ClemRz/tanduino/bitmaps/P1200767.JPG

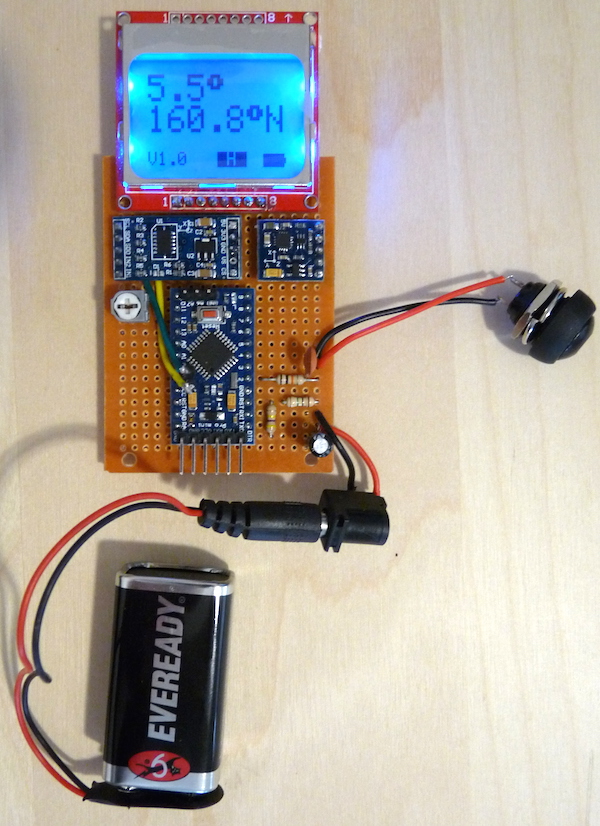
bitmaps/P1200767.JPG
