ClemRz/tanduino/bitmaps/P1200768.JPG

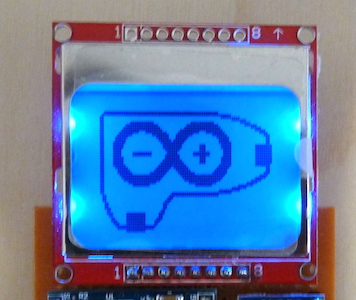
bitmaps/P1200768.JPG
