ClemRz/tanduino/bitmaps/P1200815.JPG

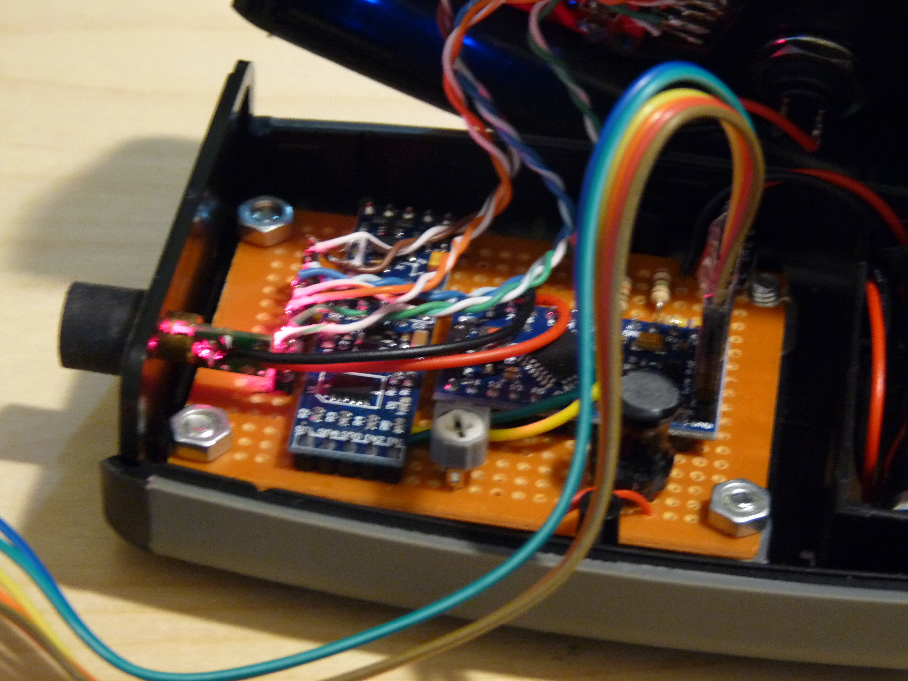
bitmaps/P1200815.JPG
