ClemRz/tanduino/bitmaps/P1200817.JPG

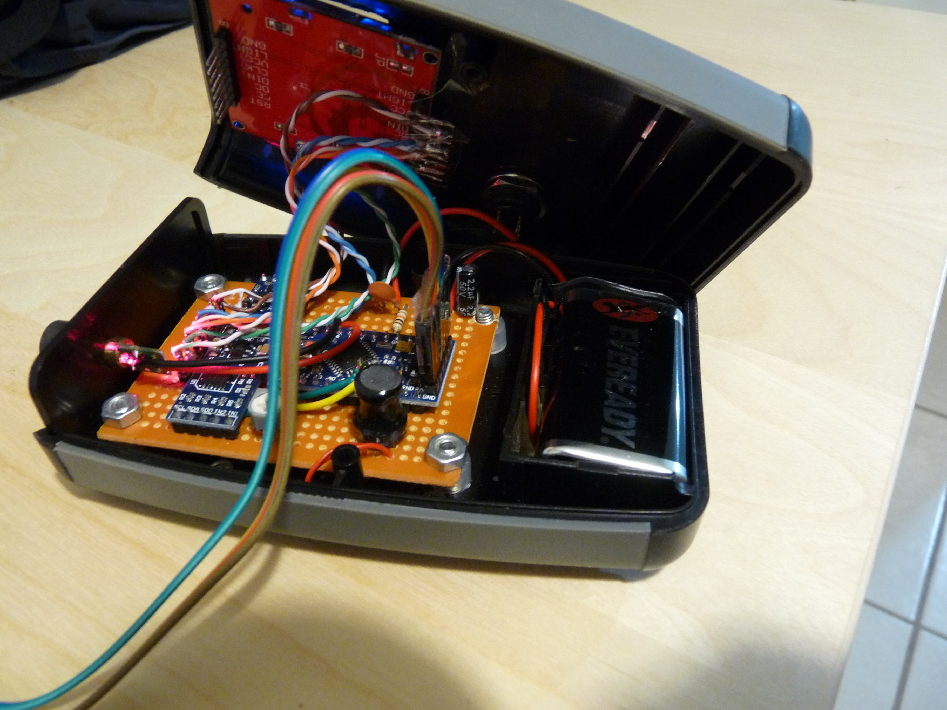
bitmaps/P1200817.JPG
