ClemRz/tanduino/bitmaps/P1200818.JPG

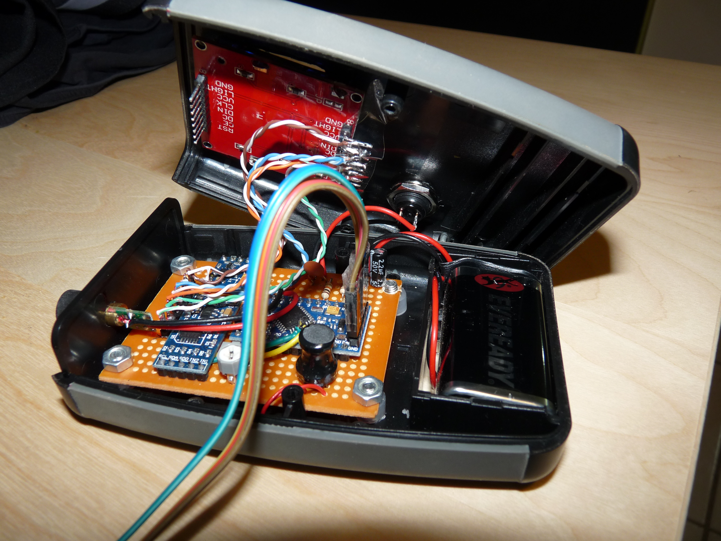
bitmaps/P1200818.JPG
